hilderonny/servotester/pictures/photo1.jpg

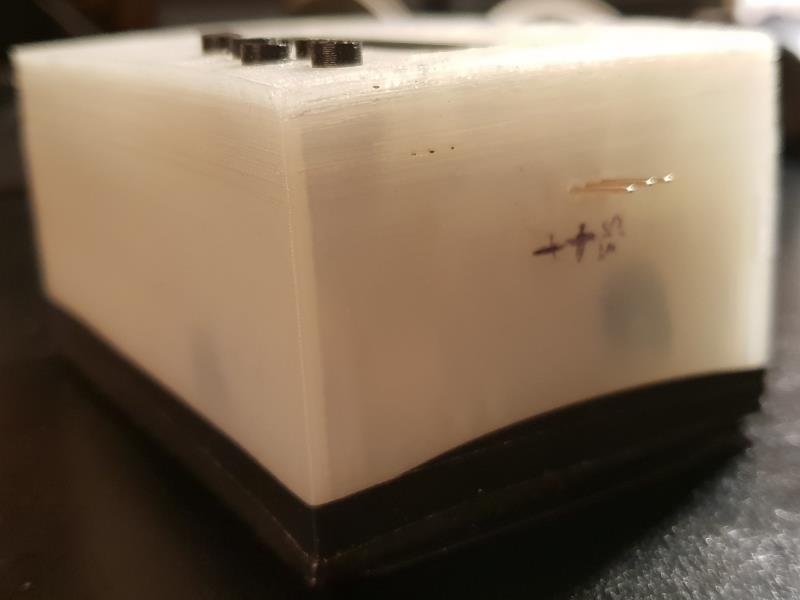
pictures/photo1.jpg
