hilderonny/servotester/pictures/photo2.jpg

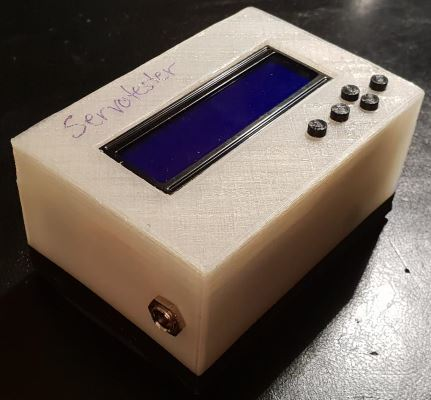
pictures/photo2.jpg
