hilderonny/servotester/pictures/photo3.jpg

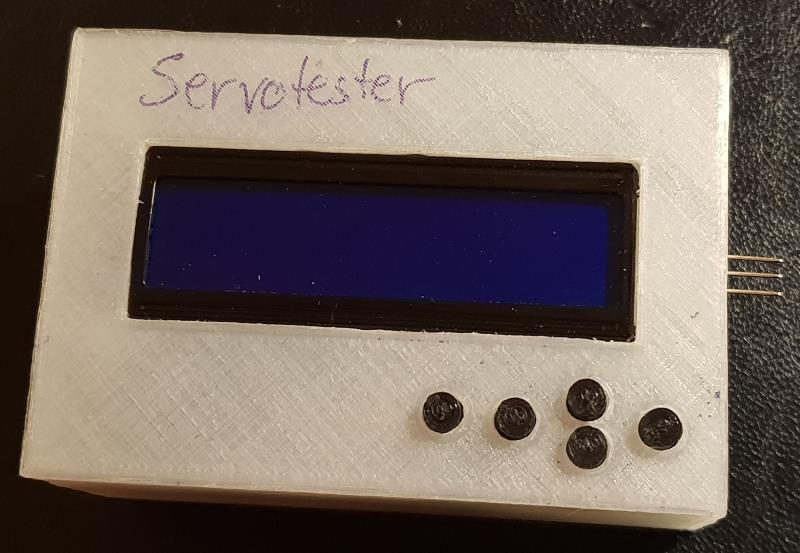
pictures/photo3.jpg
